GhanGhan/Music_Visualizer/Spectrum_Filters/RealBassFilter.asc

C1: cap; 13n
C2: cap; 13n
C3: cap; 6.8n
C4: cap; 6.8n
C5: cap; 24n
C6: cap; 24n
R1: res; 111k
R2: res; 118k
R3: res; 90.7k
R4: res; 63.5k
R5: res; 62.2k
R6: res; 312k
R7: res; 67.6k
R8: res; 66.2k
R9: res; 332k
R10: res; 163k
U1: opamp2; LM324
U2: opamp2; LM324
U3: opamp2; LM324
V1: voltage; SINE(0 0.317 260); AC 1
Vcc1: voltage; 5
Vee1: voltage; 5
Named nets: 0, F1, F2, Vi, F3, Vee, Vcc
.tran 0.05
;ac dec 100 1 1000
.include LM324.txt
