GhanGhan/Music_Visualizer/Spectrum_Filters/RealSubBassFilter.asc

C1: cap; 47n
C2: cap; 47n
C3: cap; 27n
C4: cap; 27n
C5: cap; 75n
C6: cap; 75n
R1: res; 84.6k
R2: res; 160k
R3: res; 169k
R4: res; 90k
R5: res; 37k
R6: res; 405k
R7: res; 86.7k
R8: res; 35.6k
R9: res; 390k
U1: opamp2; LM324
U2: opamp2; LM324
U3: opamp2; LM324
V1: voltage; SINE(0 0.317 55); AC 1
Vcc: voltage; 5
Vee: voltage; 5
Named nets: 0, F1, F2, Vi, F3, Vee, Vcc
.tran 1
;ac dec 100 1 250
