GhanGhan/Music_Visualizer/Spectrum_Filters/RealLowMidrange.asc

C1: cap; 13n
C2: cap; 13n
C3: cap; 6.8n
C4: cap; 6.8n
C5: cap; 24n
C6: cap; 24n
R1: res; 111k
R2: res; 118k
R3: res; 90.7k
R4: res; 63.5k
R5: res; 62.2k
R6: res; 312k
R7: res; 67.6k
R8: res; 66.2k
R9: res; 332k
R10: res; 163k
U1: opamp
U2: opamp
U3: opamp
V1: voltage; SINE(0 1 260); AC 1
Named nets: 0, F1, F2, Vi, F3
;tran 0.05
.lib opamp.sub
.ac dec 100 1 1000
