GhanGhan/Music_Visualizer/Simulated_Circuits/Spectrum_Filters/Final_Filters/AllFiltersBuf.asc

C1: cap; 47n
C2: cap; 47n
C3: cap; 27n
C4: cap; 27n
C5: cap; 75n
C6: cap; 75n
C7: cap; 100µ
C8: cap; 13n
C9: cap; 13n
C10: cap; 6.8n
C11: cap; 6.8n
C12: cap; 24n
C13: cap; 24n
C14: cap; 100µ
C15: cap; 4.7n
C16: cap; 4.7n
C17: cap; 3.3n
C18: cap; 3.3n
C19: cap; 6.2n
C20: cap; 6.2n
C21: cap; 10µ
C22: cap; 1.6n
C23: cap; 1.6n
C24: cap; 1n
C25: cap; 1n
C26: cap; 3n
C27: cap; 3n
C28: cap; 10µ
C29: cap; 1n
C30: cap; 1n
C31: cap; 1n
C32: cap; 1n
C33: cap; 1n
C34: cap; 1n
C35: cap; 1µ
C36: cap; 1n
C37: cap; 1n
C38: cap; 1n
C39: cap; 1n
C40: cap; 1n
C41: cap; 1n
C42: cap; 1µ
C43: cap; 1n
C44: cap; 1n
C45: cap; 820p
C46: cap; 820p
C47: cap; 1n
C48: cap; 1n
C49: cap; 1µ
R1: res; 84.5k
R2: res; 160k
R3: res; 169k
R4: res; 90.9k
R5: res; 37.4k
R6: res; 402k
R7: res; 86.6k
R8: res; 35.7k
R9: res; 390k
R10: res; 1k
R11: res; 110k
R12: res; 118k
R13: res; 90.9k
R14: res; 63.4k
R15: res; 62k
R16: res; 309k
R17: res; 68k
R18: res; 66.5k
R19: res; 332k
R20: res; 162k
R21: res; 1k
R22: res; 137k
R23: res; 270k
R24: res; 143k
R25: res; 19.1k
R26: res; 590k
R27: res; 140k
R28: res; 18.7k
R29: res; 576k
R30: res; 45.3k
R31: res; 1k
R32: res; 100k
R33: res; 100k
R34: res; 56k
R35: res; 48.7k
R36: res; 270k
R37: res; 66.5k
R38: res; 57.6k
R39: res; 324k
R40: res; 66.5k
R41: res; 33.2k
R42: res; 1k
R43: res; 78.7k
R44: res; 160k
R45: res; 59k
R46: res; 7.87k
R47: res; 243k
R48: res; 107k
R49: res; 14.7k
R50: res; 453k
R51: res; 26.7k
R52: res; 1k
R53: res; 78.7k
R54: res; 160k
R55: res; 66.5k
R56: res; 2.87k
R57: res; 270k
R58: res; 95.3k
R59: res; 4.02k
R60: res; 383k
R61: res; 7.32k
R62: res; 1k
R63: res; 11.5k
R64: res; 22.6k
R65: res; 8.06k
R66: res; 4.32k
R67: res; 37.4k
R68: res; 19.6k
R69: res; 10.7k
R70: res; 90.9k
R71: res; 48.7k
R72: res; 1k
U1: opamp2; LM324
U2: opamp2; LM324
U3: opamp2; LM324
U4: opamp2; LM324
U5: opamp2; LM324
U6: opamp2; LM324
U7: opamp2; LM324
U8: opamp2; LM324
U9: opamp2; LM324
U10: opamp2; LM324
U11: opamp2; LM324
U12: opamp2; LM324
U13: opamp2; LM324
U14: opamp2; LM324
U15: opamp2; LM324
U16: opamp2; LM324
U17: opamp2; LM324
U18: opamp2; LM324
U19: opamp2; LM324
U20: opamp2; LM324
U21: opamp2; LM324
U22: opamp2; LM324
U23: opamp2; LM324
U24: opamp2; LM324
U25: opamp2; LM324
U26: opamp2; LM324
U27: opamp2; LM324
U28: opamp2; LM324
V0: voltage; SINE(0 1 1000 0 0 0); AC 1
V1: voltage; SINE(0 0.5 40); AC 1
V2: voltage; SINE(0 0.5 155); AC 1
V3: voltage; SINE(0 0.5 375); AC 1
V4: voltage; SINE(0 0.5 1250); AC 1
V5: voltage; SINE(0 0.5 3000); AC 1
V6: voltage; SINE(0 0.5 5000); AC 1
V7: voltage; SINE(0 0.75 13000); AC 1
Vcc1: voltage; 5
Vee1: voltage; 5
Named nets: 0, Vi, Vee, Vcc, Sub-Bass, Bass, LowMid, Mid, UpMid, Pres, Brill
;tran .01
.ac dec 100 20 20000
[20Hz to 60Hz]
.include LM324.txt
Sub-Bass
Bass
Lower-Midrange
Midrange
Upper-Midrange
Presence
Brilliance
