GhanGhan/Music_Visualizer/Simulated_Circuits/Spectrum_Filters/Final_Filters/FinalBassFilterBUF.asc

C1: cap; 13n
C2: cap; 13n
C3: cap; 6.8n
C4: cap; 6.8n
C5: cap; 24n
C6: cap; 24n
C7: cap; 100µ
R1: res; 110k
R2: res; 90.9k
R3: res; 162k
R4: res; 118k
R5: res; 63.4k
R6: res; 62k
R7: res; 309k
R8: res; 68k
R9: res; 66.5k
R10: res; 332k
R11: res; 1k
U1: opamp2; LM324
U2: opamp2; LM324
U3: opamp2; LM324
U4: opamp2; LM324
V1: voltage; SINE(0 1 155); AC 1
Vcc: voltage; 5
Vee: voltage; 5
Named nets: 0, F1, F2, Vi, F3, Vee, Vcc, Vo
.tran 0.05
;ac dec 100 1 1000
.include LM324.txt
[60Hz to 250Hz]
