GhanGhan/Music_Visualizer/Simulated_Circuits/Spectrum_Filters/Final_Filters/FinalBrillianceFilterBUF.asc

C1: cap; 1n
C2: cap; 1n
C3: cap; 820p
C4: cap; 820p
C5: cap; 1n
C6: cap; 1n
C7: cap; 1µ
R1: res; 11.5k
R2: res; 48.7k
R3: res; 22.6k
R4: res; 8.06k
R5: res; 4.32k
R6: res; 37.4k
R7: res; 19.6k
R8: res; 10.7k
R9: res; 90.9k
R10: res; 1k
U1: opamp2; LM324
U2: opamp2; LM324
U3: opamp2; LM324
U4: opamp2; LM324
V1: voltage; SINE(0 1 13000); AC 1
Vcc: voltage; 5
Vee: voltage; 5
Named nets: 0, F1, F2, Vi, F3, Vcc, Vee, Vo
.tran 0.001
;ac dec 1000 1000 100000
[6kHz to 20kHz]
.include LM324.txt
