GhanGhan/Music_Visualizer/Simulated_Circuits/Spectrum_Filters/Final_Filters/FinalLowMidrangeBUF.asc

C1: cap; 4.7n
C2: cap; 4.7n
C3: cap; 3.3n
C4: cap; 3.3n
C5: cap; 6.2n
C6: cap; 6.2n
C7: cap; 10µ
R1: res; 137k
R2: res; 45.3k
R3: res; 270k
R4: res; 143k
R5: res; 19.1k
R6: res; 590k
R7: res; 140k
R8: res; 18.7k
R9: res; 576k
R10: res; 1k
U1: opamp2; LM324
U2: opamp2; LM324
U3: opamp2; LM324
U4: opamp2; LM324
V1: voltage; SINE(0 1 375); AC 1
Vcc: voltage; 5
Vee: voltage; 5
Named nets: 0, F1, F2, Vi, F3, Vee, Vcc, Vo
.tran 0.05
.include LM324.txt
;ac dec 100 100 1000
[250Hz to 500Hz]
