GhanGhan/Music_Visualizer/Simulated_Circuits/Spectrum_Filters/Final_Filters/FinalMidrangeFilterBUF.asc

C1: cap; 1.6n
C2: cap; 1.6n
C3: cap; 1n
C4: cap; 1n
C5: cap; 3n
C6: cap; 3n
C7: cap; 10µ
R1: res; 100k
R2: res; 100k
R3: res; 66.5k
R4: res; 33.2k
R5: res; 56k
R6: res; 48.7k
R7: res; 270k
R8: res; 66.5k
R9: res; 57.6k
R10: res; 324k
R11: res; 1k
U1: opamp2; LM324
U2: opamp2; LM324
U3: opamp2; LM324
U4: opamp2; LM324
V1: voltage; SINE(0 1 1250); AC 1
Vcc: voltage; 5
Vee: voltage; 5
Named nets: 0, F1, F2, Vi, F3, Vcc, Vee, Vo
.tran 0.01
;ac dec 100 100 4000
[500Hz to 2kHz]
.include LM324.txt
