GhanGhan/Music_Visualizer/Simulated_Circuits/Spectrum_Filters/Final_Filters/FinalPresenceFilterBUF.asc

C1: cap; 1n
C2: cap; 1n
C3: cap; 1n
C4: cap; 1n
C5: cap; 1n
C6: cap; 1n
C7: cap; 1µ
R1: res; 78.7k
R2: res; 7.32k
R3: res; 160k
R4: res; 66.5k
R5: res; 2.87k
R6: res; 270k
R7: res; 95.3k
R8: res; 4.02k
R9: res; 383k
R10: res; 1k
U1: opamp2; LM324
U2: opamp2; LM324
U3: opamp2; LM324
U4: opamp2; LM324
V1: voltage; SINE(0 1 5000); AC 1
Vcc: voltage; 5
Vee: voltage; 5
Named nets: 0, F1, F2, Vi, F3, Vcc, Vee, Vo
.tran 0.002
;ac dec 1000 2000 10000
[4kHz to 6kHz]
.include LM324.txt
