GhanGhan/Music_Visualizer/Simulated_Circuits/Spectrum_Filters/Final_Filters/FinalSubBassFilterBUF.asc

C1: cap; 47n
C2: cap; 47n
C3: cap; 27n
C4: cap; 27n
C5: cap; 75n
C6: cap; 75n
C7: cap; 100µ
R1: res; 84.5k
R2: res; 160k
R3: res; 169k
R4: res; 90.9k
R5: res; 37.4k
R6: res; 402k
R7: res; 86.6k
R8: res; 35.7k
R9: res; 390k
R10: res; 1k
U1: opamp2; LM324
U2: opamp2; LM324
U3: opamp2; LM324
U4: opamp2; LM324
V1: voltage; SINE(0 3 40); AC 1
Vcc: voltage; 5
Vee: voltage; 5
Named nets: 0, F1, F2, Vi, F3, Vee, Vcc, Vo
.tran .25
;ac dec 100 10 100
[20Hz to 60Hz]
.include LM324.txt
