GhanGhan/Music_Visualizer/Simulated_Circuits/Spectrum_Filters/Ideal_Filters/SubBassFilterSK.asc

C1: cap; 47n
C2: cap; 47n
C3: cap; 27n
C4: cap; 27n
C5: cap; 75n
C6: cap; 75n
R1: res; 84.6k
R2: res; 160k
R3: res; 169k
R4: res; 90k
R5: res; 37k
R6: res; 405k
R7: res; 86.7k
R8: res; 35.6k
R9: res; 390k
U1: opamp
U2: opamp
U3: opamp
V1: voltage; SINE(0 1 55); AC 1
Named nets: 0, F1, F2, Vi, F3
.lib opamp.sub
;tran 1
.ac dec 100 10 100
[20Hz to 60Hz]
