GhanGhan/Music_Visualizer/Simulated_Circuits/Spectrum_Filters/Ideal_Filters/BrillianceFilterSK.asc

C1: cap; 1n
C2: cap; 1n
C3: cap; 820p
C4: cap; 820p
C5: cap; 1n
C6: cap; 1n
R1: res; 11.4k
R2: res; 48.8k
R3: res; 22.7k
R4: res; 8.02k
R5: res; 4.35k
R6: res; 37k
R7: res; 19.6k
R8: res; 10.6k
R9: res; 90.5k
U1: opamp
U2: opamp
U3: opamp
V1: voltage; SINE(0 1 260); AC 1
Named nets: 0, F1, F2, Vi, F3
;tran 0.05
.lib opamp.sub
.ac dec 1000 1000 100000
[6kHz to 20kHz]
