GhanGhan/Music_Visualizer/Simulated_Circuits/Spectrum_Filters/Ideal_Filters/LowMidrangeFilterSK.asc

C1: cap; 4.7n
C2: cap; 4.7n
C3: cap; 3.3n
C4: cap; 3.3n
C5: cap; 6.2n
C6: cap; 6.2n
R1: res; 135k
R2: res; 45.1k
R3: res; 271k
R4: res; 142k
R5: res; 19.2k
R6: res; 595k
R7: res; 139k
R8: res; 18.9k
R9: res; 583k
U1: opamp
U2: opamp
U3: opamp
V1: voltage; SINE(0 1 260); AC 1
Named nets: 0, F1, F2, Vi, F3
;tran 0.05
.lib opamp.sub
.ac dec 100 100 1000
[250Hz to 500Hz]
