GhanGhan/Music_Visualizer/Simulated_Circuits/Spectrum_Filters/Ideal_Filters/MidrangeFilterSK.asc

C1: cap; 1.6n
C2: cap; 1.6n
C3: cap; 1n
C4: cap; 1n
C5: cap; 3n
C6: cap; 3n
R1: res; 99.7k
R2: res; 65.8k
R3: res; 99.2k
R4: res; 55.9k
R5: res; 48.6k
R6: res; 271k
R7: res; 67k
R8: res; 58.2k
R9: res; 325k
R10: res; 33.2k
U1: opamp
U2: opamp
U3: opamp
V1: voltage; SINE(0 1 260); AC 1
Named nets: 0, F1, F2, Vi, F3
;tran 0.05
.lib opamp.sub
.ac dec 100 100 4000
[500Hz to 2kHz]
