GhanGhan/Music_Visualizer/Simulated_Circuits/Spectrum_Filters/Ideal_Filters/PresenceFilterSK.asc

C1: cap; 1n
C2: cap; 1n
C3: cap; 1n
C4: cap; 1n
C5: cap; 1n
C6: cap; 1n
R1: res; 79.5k
R2: res; 7.24k
R3: res; 159k
R4: res; 66.6k
R5: res; 2.85k
R6: res; 271k
R7: res; 94.9k
R8: res; 4.06k
R9: res; 386k
U1: opamp
U2: opamp
U3: opamp
V1: voltage; SINE(0 1 260); AC 1
Named nets: 0, F1, F2, Vi, F3
;tran 0.05
.lib opamp.sub
.ac dec 1000 2000 10000
[4kHz to 6kHz]
