GhanGhan/Music_Visualizer/Simulated_Circuits/Spectrum_Filters/Ideal_Filters/UpperMidrangeFilterSK.asc

C1: cap; 1n
C2: cap; 1n
C3: cap; 1n
C4: cap; 1n
C5: cap; 1n
C6: cap; 1n
R1: res; 79.5k
R2: res; 26.5k
R3: res; 159k
R4: res; 58.6k
R5: res; 7.94k
R6: res; 245k
R7: res; 108k
R8: res; 14.6k
R9: res; 452k
U1: opamp
U2: opamp
U3: opamp
V1: voltage; SINE(0 1 260); AC 1
Named nets: 0, F1, F2, Vi, F3
;tran 0.05
.lib opamp.sub
.ac dec 100 1000 10000
[2kHz to 4kHz]
