GhanGhan/Music_Visualizer/Misc/LT1054_Inverter_and_regulator.asc

C1: cap; 1µ
C2: cap; 1µ
C5: polcap; 10µ
C7: polcap; 0.002µ
C8: polcap; 100µ
R1: res; 20k
R2: res; 102k
R3: res; 330
U1: LT1054
V1: voltage; 9
Named nets: 0, Vout, VFb, Vref, Vin
.tran 30m uic
