GhanGhan/Music_Visualizer/RhiControl/RhiControl_LTC1250.asc

R1: res; 10k
R2: res; 10
R3: res; 2.5k
U1: LTC1250
V1: voltage; 5
Vcc: voltage; 5
Vee: voltage; -5
Named nets: Vcc, 0, Vin, Vout, Vee
.tran .05
