GhanGhan/Music_Visualizer/Misc/Bridge Rectifier.asc

D1: diode
D2: diode
D3: diode
D4: diode
R1: res; 100
V2: battery; SINE(0 5 20); AC 10
Named nets: Vin, Rout, 0
.tran 1
