GhanGhan/Music_Visualizer/Simulated_Circuits/LED_Driving/LM3915_Base_Circuit.asc

C1: cap; 220µ
D1: LED; NSCW100
D2: LED; NSCW100
D3: LED; NSCW100
D4: LED; NSCW100
D5: LED; NSCW100
D6: LED; NSCW100
D7: LED; NSCW100
D8: LED; NSCW100
D9: LED; NSCW100
D10: LED; NSCW100
R4: res; 674
U3: lm3915
V2: voltage; SINE(0 2 50)
Vcc: voltage; 9
Vrhi: voltage; 3.5
Named nets: 0, Vs, LED1, LED2, LED3, LED4, LED5, LED6, LED7, LED8, LED9, LED10, Vref
.tran 0.1
