GhanGhan/Music_Visualizer/Simulated_Circuits/LED_Driving/LM3915_Chain.asc

C1: cap; 220µ
C3: cap; 220µ
C4: cap; 220µ
C5: cap; 220µ
C6: cap; 220µ
C7: cap; 220µ
C8: cap; 220µ
D1: LED; NSCW100
D2: LED; NSCW100
D3: LED; NSCW100
D4: LED; NSCW100
D5: LED; NSCW100
D6: LED; NSCW100
D7: LED; NSCW100
D8: LED; NSCW100
D9: LED; NSCW100
D10: LED; NSCW100
D12: LED; NSCW100
D13: LED; NSCW100
D14: LED; NSCW100
D15: LED; NSCW100
D16: LED; NSCW100
D17: LED; NSCW100
D18: LED; NSCW100
D19: LED; NSCW100
D20: LED; NSCW100
D21: LED; NSCW100
D22: LED; NSCW100
D23: LED; NSCW100
D24: LED; NSCW100
D25: LED; NSCW100
D26: LED; NSCW100
D27: LED; NSCW100
D28: LED; NSCW100
D29: LED; NSCW100
D30: LED; NSCW100
D31: LED; NSCW100
D32: LED; NSCW100
D33: LED; NSCW100
D34: LED; NSCW100
D35: LED; NSCW100
D36: LED; NSCW100
D37: LED; NSCW100
D38: LED; NSCW100
D39: LED; NSCW100
D40: LED; NSCW100
D41: LED; NSCW100
D42: LED; NSCW100
D43: LED; NSCW100
D44: LED; NSCW100
D45: LED; NSCW100
D46: LED; NSCW100
D47: LED; NSCW100
D48: LED; NSCW100
D49: LED; NSCW100
D50: LED; NSCW100
D51: LED; NSCW100
D52: LED; NSCW100
D53: LED; NSCW100
D54: LED; NSCW100
D55: LED; NSCW100
D56: LED; NSCW100
D57: LED; NSCW100
D58: LED; NSCW100
D59: LED; NSCW100
D60: LED; NSCW100
D61: LED; NSCW100
D62: LED; NSCW100
D63: LED; NSCW100
D64: LED; NSCW100
D65: LED; NSCW100
D66: LED; NSCW100
D67: LED; NSCW100
D68: LED; NSCW100
D69: LED; NSCW100
D70: LED; NSCW100
D71: LED; NSCW100
R2: res; 115k
R3: res; 5k
R4: res; 680
R5: res; 680
R6: res; 680
R7: res; 680
R8: res; 680
R9: res; 680
R10: res; 680
RadjPot: res; 0
U1: lm3915
U3: lm3915
U4: lm3915
U5: lm3915
U6: lm3915
U7: lm3915
U8: lm3915
V2: voltage; SINE(0 0.063 50)
Vcc: voltage; 9
Named nets: 0, Vcc, Vi, LED1, LED2, LED3, LED4, LED5, LED6, LED7, LED8, LED9, LED10, Vref1, Vrhi, Vref2, Vref3, Vref4, Vref5, Vref6, Vref7
.tran 0.1
Pot = [0:10kohm],
