GhanGhan/Music_Visualizer/Simulated_Circuits/Filters_With_LED_Drivers/FinalUpperMidrangeFilterWithLEDDriver.asc

C1: cap; 1n
C2: cap; 1n
C3: cap; 1n
C4: cap; 1n
C5: cap; 1n
C6: cap; 1n
C7: cap; 1µ
C8: cap; 220µ
D1: LED; NSCW100
D2: LED; NSCW100
D3: LED; NSCW100
D4: LED; NSCW100
D5: LED; NSCW100
D6: LED; NSCW100
D7: LED; NSCW100
D8: LED; NSCW100
D9: LED; NSCW100
D10: LED; NSCW100
R1: res; 78.7k
R2: res; 26.5k
R3: res; 159k
R4: res; 59k
R5: res; 7.87k
R6: res; 243k
R7: res; 107k
R8: res; 14.7k
R9: res; 453k
R10: res; 1k
R11: res; 680
R12: res; 10k
R13: res; 1k
U1: opamp2; LM324
U2: opamp2; LM324
U3: opamp2; LM324
U4: lm3915
U5: LTC1250
V1: voltage; SINE(0 0.2 3000); AC 1
Vcc: voltage; 5
Vee: voltage; 5
Vps: voltage; 9
Named nets: 0, F1, F2, Vs, F3, Vcc, Vee, Vi, Vps, LED1, LED2, LED3, LED4, LED5, LED6, LED7, LED8, LED9, LED10, Vref, Vin, VRhi
.tran 0.002
;ac dec 100 1000 10000
[2kHz to 4kHz]
.include LM324.txt
