GhanGhan/Music_Visualizer/Simulated_Circuits/LED_Driving/Voltage_Follower_Replacement.asc

Q1: npn; 2N2222
R1: res; 2500
R2: res; 1000
R3: res; 4000
V1: voltage; 5
V2: voltage; SINE(0 3.5 0.5)
V3: voltage; 3.5
Named nets: Vcc, 0, Vout, Vin
.tran 1
Q1 is used to replace op-amp in RhiControl circuit since power termianls of
op-amp someohow shorted together, input voltage needs to be at least 0.658
volts to turn on
