GhanGhan/Music_Visualizer/Simulated_Circuits/LED_Driving/RhiControl_LTC1250.asc

R1: res; 10k
R2: res; 10
R3: res; 2.5k
U1: LTC1250
V1: voltage; 5
Vcc: voltage; 5
Vee: voltage; -5
Named nets: Vcc, 0, Vin, Vout, Vee
.tran .05
Need negative power terminal to be powered by -5V instead of ground
because outpute of voltage follower won't be accurate to the mV otherwise.
For R2 = 10, and R1 = 10kohm, Vo=Vi = 4.995mV.  However if the negative
power terminal were grounded, Vo = 193mV
Also, this op-amp has an input offset voltage of max |10uV|, so there will not
be unintnted LED activation of potemiomter set to 0V.
