GhanGhan/Music_Visualizer/Simulated_Circuits/Entire_Circuit/Full_Visualizer.asc

C1: cap; 47n
C2: cap; 47n
C3: cap; 27n
C4: cap; 27n
C5: cap; 75n
C6: cap; 75n
C7: cap; 13n
C8: cap; 13n
C9: cap; 6.8n
C10: cap; 6.8n
C11: cap; 24n
C12: cap; 24n
C13: cap; 4.7n
C14: cap; 4.7n
C15: cap; 3.3n
C16: cap; 3.3n
C17: cap; 6.2n
C18: cap; 6.2n
C19: cap; 1.6n
C20: cap; 1.6n
C21: cap; 1n
C22: cap; 1n
C23: cap; 3n
C24: cap; 3n
C25: cap; 1n
C26: cap; 1n
C27: cap; 1n
C28: cap; 1n
C29: cap; 1n
C30: cap; 1n
C31: cap; 1n
C32: cap; 1n
C33: cap; 1n
C34: cap; 1n
C35: cap; 1n
C36: cap; 1n
C37: cap; 1n
C38: cap; 1n
C39: cap; 820p
C40: cap; 820p
C41: cap; 1n
C42: cap; 1n
C43: cap; 220µ
D1: LED; NSCW100
D2: LED; NSCW100
D3: LED; NSCW100
D4: LED; NSCW100
D5: LED; NSCW100
D6: LED; NSCW100
D7: LED; NSCW100
D8: LED; NSCW100
D9: LED; NSCW100
D10: LED; NSCW100
D11: LED; NSCW100
D12: LED; NSCW100
D13: LED; NSCW100
D14: LED; NSCW100
D15: LED; NSCW100
D16: LED; NSCW100
D17: LED; NSCW100
D18: LED; NSCW100
D19: LED; NSCW100
D20: LED; NSCW100
D21: LED; NSCW100
D22: LED; NSCW100
D23: LED; NSCW100
D24: LED; NSCW100
D25: LED; NSCW100
D26: LED; NSCW100
D27: LED; NSCW100
D28: LED; NSCW100
D29: LED; NSCW100
D30: LED; NSCW100
D31: LED; NSCW100
D32: LED; NSCW100
D33: LED; NSCW100
D34: LED; NSCW100
D35: LED; NSCW100
D36: LED; NSCW100
D37: LED; NSCW100
D38: LED; NSCW100
D39: LED; NSCW100
D40: LED; NSCW100
D41: LED; NSCW100
D42: LED; NSCW100
D43: LED; NSCW100
D44: LED; NSCW100
D45: LED; NSCW100
D46: LED; NSCW100
D47: LED; NSCW100
D48: LED; NSCW100
D49: LED; NSCW100
D50: LED; NSCW100
D51: LED; NSCW100
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
.tran 5m
;ac dec 100 1 250
[20Hz to 60Hz]
.include LM324.txt
[60Hz to 250Hz]
[250Hz to 500Hz]
[500Hz to 2kHz]
[2kHz to 4kHz]
[4kHz to 6kHz]
[6kHz to 20kHz]
Leftover Op-Amps (Cause there are 4 in one IC)
Pot = [0:10kohm],
