GhanGhan/Music_Visualizer/Simulated_Circuits/Power/Reverse_Voltage_Protection.asc

M1: pmos; RTR025P02
R1: res; 200
V1: voltage; 9
Named nets: 0, IN, Load
.tran 1
