GhanGhan/Music_Visualizer/Simulated_Circuits/Filters_With_LED_Drivers/FinalSubBassFilterWithLEDDriver.asc

C1: cap; 47n
C2: cap; 47n
C3: cap; 27n
C4: cap; 27n
C5: cap; 75n
C6: cap; 75n
C7: cap; 100µ
C8: cap; 220µ
D1: LED; NSCW100
D2: LED; NSCW100
D3: LED; NSCW100
D4: LED; NSCW100
D5: LED; NSCW100
D6: LED; NSCW100
D7: LED; NSCW100
D8: LED; NSCW100
D9: LED; NSCW100
D10: LED; NSCW100
R1: res; 84.5k
R2: res; 160k
R3: res; 169k
R4: res; 90.9k
R5: res; 37.4k
R6: res; 402k
R7: res; 86.6k
R8: res; 35.7k
R9: res; 390k
R10: res; 1k
R14: res; 680
R15: res; 10k
R16: res; 1k
U1: opamp2; LM324
U2: opamp2; LM324
U3: opamp2; LM324
U4: LTC1250
U5: lm3915
V1: voltage; SINE(0 3 40); AC 1
Vcc: voltage; 5
Vee: voltage; 5
Vps: voltage; 9
Named nets: 0, F1, F2, Vs, F3, Vee, Vcc, Vi, Vps, LED1, LED2, LED3, LED4, LED5, LED6, LED7, LED8, LED9, LED10, Vref, Vin, VRhi
.tran 0.25
;ac dec 100 1 250
[20Hz to 60Hz]
.include LM324.txt
