GhanGhan/Music_Visualizer/Simulated_Circuits/Filters_With_LED_Drivers/FinalLowMidrangeWithLEDDriver.asc

C1: cap; 4.7n
C2: cap; 4.7n
C3: cap; 3.3n
C4: cap; 3.3n
C5: cap; 6.2n
C6: cap; 6.2n
C7: cap; 10µ
C8: cap; 220µ
D1: LED; NSCW100
D2: LED; NSCW100
D3: LED; NSCW100
D4: LED; NSCW100
D5: LED; NSCW100
D6: LED; NSCW100
D7: LED; NSCW100
D8: LED; NSCW100
D9: LED; NSCW100
D10: LED; NSCW100
R1: res; 137k
R2: res; 45.3k
R3: res; 270k
R4: res; 143k
R5: res; 19.2k
R6: res; 590k
R7: res; 140k
R8: res; 19k
R9: res; 576k
R10: res; 1k
R11: res; 680
R12: res; 10k
R13: res; 25k
U1: opamp2; LM324
U2: opamp2; LM324
U3: opamp2; LM324
U4: lm3915
U5: LTC1250
V1: voltage; SINE(0 0.18 375); AC 1
Vcc: voltage; 5
Vee: voltage; 5
Vps: voltage; 9
Named nets: 0, F1, F2, Vs, F3, Vee, Vcc, Vi, Vps, LED1, LED2, LED3, LED4, LED5, LED6, LED7, LED8, LED9, LED10, Vref, Vin, VRhi
.tran 0.05
.include LM324.txt
;ac dec 100 100 1000
[250Hz to 500Hz]
